kayeks-elec/DMClock/Sources/display.c

/*
 * DotMatrixClock2018/display.c
 *
 *  Author: kayekss
 *  Target: ATmega328P, 20.000 MHz crystal oscillator
 */

#include <stdlib.h>
#include <avr/io.h>
#include <avr/pgmspace.h>
#include "display.h"

// Front frame buffer - to be read from display ISR
volatile uint32_t fb_front[16];
// Back frame buffer - drawing functions should write to this plane
volatile uint32_t fb_back[16];

// Index table for font "M0410"
PROGMEM uint16_t const font_index_m0410[128] = {
    // 0x00
      0,   0,   0,   0,   0,   0,   0,   0,
      0,   0,   0,   0,   0,   0,   0,   0,
    // 0x10
      0,   0,   0,   0,   0,   0,   0,   0,
      0,   0,   0,   0,   0,   0,   0,   0,
    // 0x20
     10,   0,   0,   0,   0,   0,   0,   0,
      0,   0,   0,   0,   0,  20,  30,   0,
    // 0x30
     40,  50,  60,  70,  80,  90, 100, 110,
    120, 130, 140,   0,   0,   0,   0,   0,
    // 0x40
      0,   0,   0,   0,   0,   0,   0,   0,
      0,   0,   0,   0,   0,   0,   0,   0,
    // 0x50
      0,   0,   0,   0,   0,   0,   0,   0,
      0,   0,   0,   0,   0,   0,   0,   0,
    // 0x60
      0,   0,   0,   0,   0,   0,   0,   0,
      0,   0,   0,   0,   0,   0,   0,   0,
    // 0x70
      0,   0,   0,   0,   0,   0,   0,   0,
      0,   0,   0,   0,   0,   0,   0,   0
};
// Bitmap for font "M0410"
PROGMEM uint8_t const font_bitmap_m0410[] = {
    // (+  0) unimplemented character
    0x0a, 0x05, 0x0a, 0x05, 0x0a, 0x05, 0x0a, 0x05, 0x0a, 0x05,
    // (+ 10) space
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
    // (+402) b
    3, 0x04, 0x07, 0x05, 0x05, 0x07,
    // (+408) c
    3, 0x00, 0x07, 0x04, 0x04, 0x07,
    // (+414) d
    3, 0x01, 0x07, 0x05, 0x05, 0x07,
    // (+420) e
    3, 0x00, 0x03, 0x05, 0x06, 0x03,
    // (+426) f
    2, 0x03, 0x02, 0x03, 0x02, 0x02,
    // (+432) g
    3, 0x00, 0x03, 0x05, 0x03, 0x06,
    // (+438) h
    3, 0x04, 0x07, 0x05, 0x05, 0x05,
    // (+444) i
    1, 0x01, 0x00, 0x01, 0x01, 0x01,
    // (+450) j
    2, 0x01, 0x00, 0x01, 0x01, 0x02,
    // (+456) k
    3, 0x04, 0x05, 0x06, 0x05, 0x05,
    // (+462) l
    2, 0x03, 0x01, 0x01, 0x01, 0x01,
    // (+468) m
    5, 0x00, 0x1e, 0x15, 0x15, 0x15,
    // (+474) n
    3, 0x00, 0x06, 0x05, 0x05, 0x05,
    // (+480) o
    3, 0x00, 0x07, 0x05, 0x05, 0x07,
    // (+486) p
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
    // (+576) \177 degree
    3, 0x07, 0x05, 0x07, 0x00, 0x00,
    // (+582) \200 button icon <up>
    8, 0x08, 0x1c, 0x3e, 0x00, 0x00,
    // (+588) \201 button icon <down>
    8, 0x00, 0x3e, 0x1c, 0x08, 0x00,
    // (+594) \202 button icon <next>
    8, 0x24, 0x36, 0x36, 0x24, 0x00,
    // (+600) \203 button icon <changevalue>
    8, 0x00, 0x04, 0x6e, 0x04, 0x00,
    // (+606) \204 button icon <discard>
    8, 0x24, 0x18, 0x18, 0x24, 0x00,
    // (+612) \205 button icon <save>
    8, 0x04, 0x2c, 0x38, 0x10, 0x00,
    // (+618) \206 ballot box
    5, 0x1f, 0x11, 0x11, 0x11, 0x1f,
    // (+624) \207 ballot box with check
    5, 0x1f, 0x13, 0x15, 0x19, 0x1f,
    // (+630) \210 lower single dot
    1, 0x00, 0x00, 0x00, 0x01, 0x00,
    // (+636) \211 higher single dot
    1, 0x00, 0x01, 0x00, 0x00, 0x00,
    // (+642) \212 wavedash
    4, 0x00, 0x00, 0x0d, 0x0b, 0x00,
    // (+648) \213 condensed string block "Brightness" (first quarter)
    8, 0xe2, 0xac, 0xca, 0xaa, 0xea,
    // (+654) \214 condensed string block "Brightness" (second quarter)
    8, 0x08, 0x6e, 0xaa, 0x6a, 0xca,
    // (+660) \215 condensed string block "Brightness" (third quarter)
    8, 0x80, 0xd8, 0x95, 0x95, 0xd4,
    // (+666) \216 condensed string block "Brightness" (fourth quarter)
    8, 0x00, 0xdb, 0x52, 0x89, 0xdb,
    // (+672) \217 brightness bar image <auto> (first half)
    8, 0x00, 0xff, 0xd5, 0xaa, 0xff,
    // (+678) \220 brightness bar image <auto> (last half)
    8, 0x00, 0xff, 0x55, 0xab, 0xff,
    // (+684) \221 brightness bar image <1> (first half)
    8, 0x00, 0xff, 0xf0, 0xf8, 0xff,
    // (+690) \222 brightness bar image <1> (last half)
    8, 0x00, 0xff, 0x01, 0x01, 0xff,
    // (+696) \223 brightness bar image <2..4> (first half) or <4> (last half)
    8, 0x00, 0xff, 0xff, 0xff, 0xff,
    // (+702) \224 brightness bar image <2> (last half)
    8, 0x00, 0xff, 0x01, 0x81, 0xff,
    // (+708) \225 brightness bar image <3> (last half)
    8, 0x00, 0xff, 0xf1, 0xf9, 0xff,
    // (+714) \226 condensed string block "Tracking.." (first quarter)
    8, 0xe0, 0x5b, 0x51, 0x52, 0x53,
    // (+720) \227 condensed string block "Tracking.." (second quarter)
    8, 0x04, 0x35, 0xa6, 0xa5, 0xb5,
    // (+726) \230 condensed string block "Tracking.." (third quarter)
    8, 0x40, 0x18, 0x55, 0x54, 0x55,
    // (+732) \231 condensed string block "Tracking.." (fourth quarter)
    5, 0x00, 0x18, 0x08, 0x18, 0x15,
    // (+738) \232 Dot blinker <1>
    3, 0x00, 0x03, 0x07, 0x07, 0x00,
    // (+744) \233 Dot blinker <2>
    3, 0x00, 0x05, 0x07, 0x07, 0x00,
    // (+750) \234 Dot blinker <3>
    3, 0x00, 0x06, 0x07, 0x07, 0x00,
    // (+756) \235 Dot blinker <4>
    3, 0x00, 0x07, 0x06, 0x07, 0x00,
    // (+762) \236 Dot blinker <5>
    3, 0x00, 0x07, 0x07, 0x06, 0x00,
    // (+768) \237 Dot blinker <6>
    3, 0x00, 0x07, 0x07, 0x05, 0x00,
    // (+768) \237 Dot blinker <7>,
    3, 0x00, 0x07, 0x07, 0x03, 0x00,
    // (+768) \237 Dot blinker <8>
    3, 0x00, 0x07, 0x03, 0x07, 0x00
};

// Clear back frame buffer
void display_clear() {
    for (uint8_t i = 0; i < 16; i++) {
        fb_back[i] = 0ul;
    }
}

// Synchronize frame buffer planes
void display_sync() {
    for (uint8_t i = 0; i < 16; i++) {
        fb_front[i] = fb_back[i];
    }
}

// Display a character with specified font and coordinate
void display_putc(font_t f, uint8_t x, uint8_t y, uint8_t c) {
    uint8_t cm = c;
    uint8_t height = 0;
    uint16_t index = 0;
    uint8_t width = 0;
    uint32_t b;
    uint16_t bitmap_base = 0;
    volatile uint32_t *fbp = NULL;

    // Setup parameters
    switch (f) {
    case FONT_M0410:
        height = 10;
        index = pgm_read_word(font_index_m0410 + cm);
        width = 4;
        bitmap_base = (uint16_t) font_bitmap_m0410;
        break;
    case FONT_M0610:
        height = 10;
        index = pgm_read_word(font_index_m0610 + cm);
        width = 6;
        bitmap_base = (uint16_t) font_bitmap_m0610;
        break;
    case FONT_PP05:
        height = 5;
        index = pgm_read_word(font_index_pp05 + cm);
        width = pgm_read_byte(font_wbitmap_pp05 + index);
        bitmap_base = (uint16_t) font_wbitmap_pp05;
        break;
    }
    // Iterate for lines
    for (uint8_t i = 0; i < height; i++) {
        // Get destination of frame buffer to write
        fbp = &fb_back[y + i];
        // Get bitmap line
        if ((f & FONT_MASK) == FONT_PROPORTIONAL) {
            // For proportional fonts, add 1 width byte to the bitmap address
            b = pgm_read_byte(bitmap_base + index + 1 + i);
        } else {
            b = pgm_read_byte(bitmap_base + index + i);
        }
        // Overlay to back frame buffer
        if (x < width - 1) {
            *fbp |= b >> ((width - 1) - x);
        } else {
            *fbp |= b << (x - (width - 1));
        }
    }
}

// Display a vertically-scrolling character with specified font and coordinate
void display_putc_scroll(font_t f, uint8_t x, uint8_t y, uint8_t c_ex,
    uint8_t c_new, uint8_t frame) {
    uint8_t cm_ex = c_ex;
    uint8_t cm_new = c_new;
    uint8_t height = 0;
    uint16_t index_ex = 0, index_new = 0;
    uint8_t width_ex = 0, width_new = 0;
    uint32_t b;
    uint16_t bitmap_base = 0;
    volatile uint32_t *fbp = NULL;

    // Setup parameters
    switch (f) {
    case FONT_M0410:
        height = 10;
        index_ex = pgm_read_word(font_index_m0410 + cm_ex);
        index_new = pgm_read_word(font_index_m0410 + cm_new);
        width_ex = 4;
        width_new = 4;
        bitmap_base = (uint16_t) font_bitmap_m0410;
        break;
    case FONT_M0610:
        height = 10;
        index_ex = pgm_read_word(font_index_m0610 + cm_ex);
        index_new = pgm_read_word(font_index_m0610 + cm_new);
        width_ex = 6;
        width_new = 6;
        bitmap_base = (uint16_t) font_bitmap_m0610;
        break;
    case FONT_PP05:
        height = 5;
        index_ex = pgm_read_word(font_index_pp05 + cm_ex);
        index_new = pgm_read_word(font_index_pp05 + cm_new);
        width_ex = pgm_read_byte(font_wbitmap_pp05 + index_ex);
        width_new = pgm_read_byte(font_wbitmap_pp05 + index_new);
        bitmap_base = (uint16_t) font_wbitmap_pp05;
        break;
    }
    // Do nothing in case of invalid frame count
    if (frame > height) {
        return;
    }
    // Iterate for lines in new character
    for (uint8_t i = 0; i < frame - 1; i++) {
        // Get destination of frame buffer to write
        fbp = &fb_back[y + i];
        // Get bitmap line
        if (f == FONT_PP05) {
            // For proportional fonts, add 1 width byte to the bitmap address
            b = pgm_read_byte(bitmap_base + index_new + 1
                + (height + 1 - frame + i));
        } else {
            b = pgm_read_byte(bitmap_base + index_new
                + (height + 1 - frame + i));
        }
        // Overlay to back frame buffer
        if (x < width_new - 1) {
            *fbp |= b >> ((width_new - 1) - x);
        } else {
            *fbp |= b << (x - (width_new - 1));
        }
    }
    // Iterate for lines in existing character
    for (uint8_t i = 0; i < height - frame; i++) {
        // Get destination of frame buffer to write
        fbp = &fb_back[y + frame + i];
        // Get bitmap line
        if ((f & FONT_MASK) == FONT_PROPORTIONAL) {
            // For proportional fonts, add 1 width byte to the bitmap address
            b = pgm_read_byte(bitmap_base + index_ex + 1 + i);
        } else {
            b = pgm_read_byte(bitmap_base + index_ex + i);
        }
        // Overlay to back frame buffer
        if (x < width_ex - 1) {
            *fbp |= b >> ((width_ex - 1) - x);
        } else {
            *fbp |= b << (x - (width_ex - 1));
        }
    }
}
